unparallel-innovation/UI_Waziup_Weather_Station/SensorHumidity.cpp

#include "SensorHumidity.h"


//Initialize
SensorHumidity::SensorHumidity()
{

}

	//------------------------------- Begin Humidity sensor -------------------------------------
	int SensorHumidity::begin()
	{
		SPI.begin();

		#ifdef USE_SI7021
			if(si70.begin()!=0)
				return 0;
			else
				return 1;
		#endif

		#ifdef USE_AM2315
			if(am23.begin())
			{
				delay(100);
				return 0;
			}
			else
				return 1;
		#endif
	}
	//----------------------------------------------------------------------------------------------

	//--------------------------------------	Get Humidity ---------------------------------------
	float SensorHumidity::getHumidity()
	{
		#ifdef USE_SI7021
			return si70.getRH();
		#endif

		#ifdef USE_AM2315
			float humidity = am23.readHumidity();
			delay(100);
			return humidity;
		#endif
	}
	//----------------------------------------------------------------------------------------------
